WillACosta/wlfkbd/docs/gallery/IMG_1042.JPEG

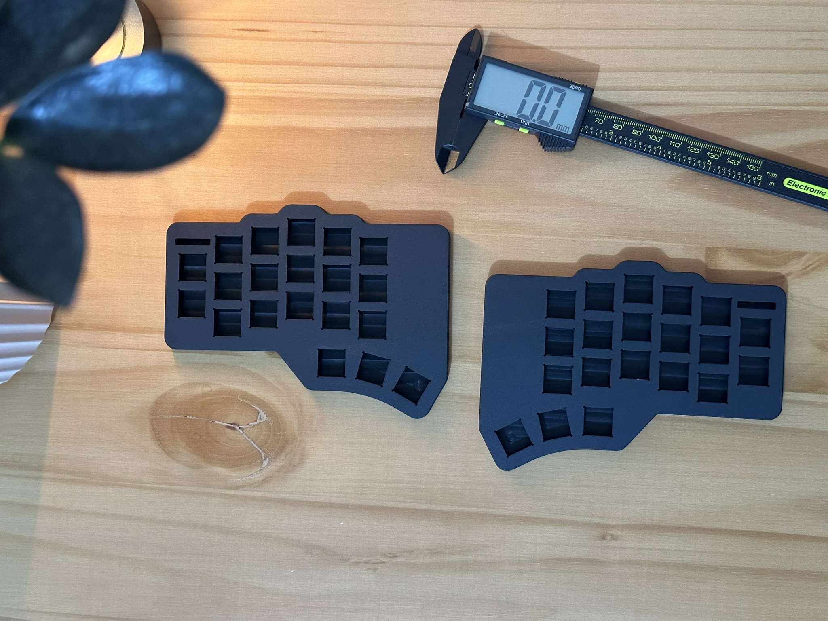
docs/gallery/IMG_1042.JPEG
