WillACosta/wlfkbd/docs/gallery/IMG_1050.JPEG

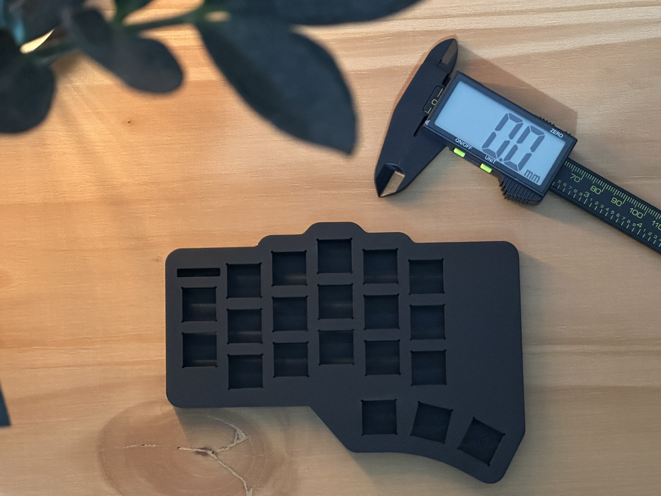
docs/gallery/IMG_1050.JPEG
