WillACosta/wlfkbd/docs/gallery/IMG_1052.JPEG

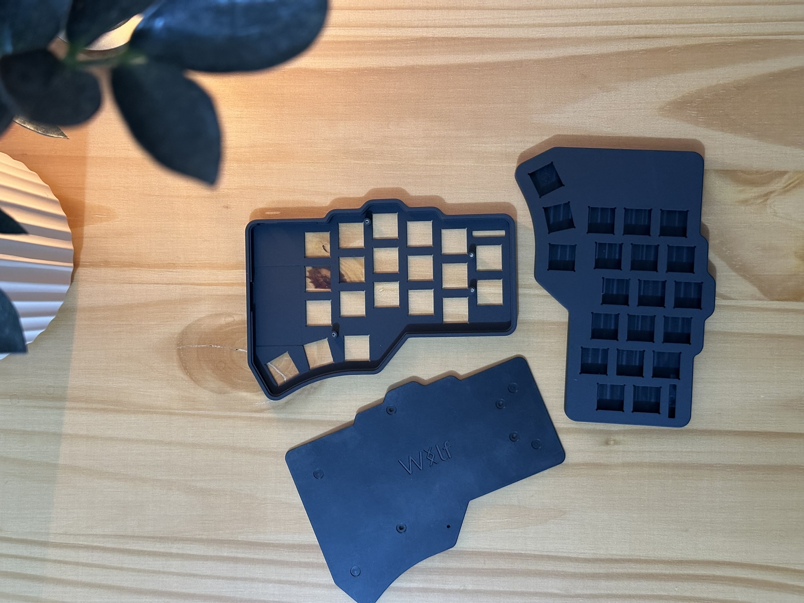
docs/gallery/IMG_1052.JPEG
