WillACosta/wlfkbd/docs/gallery/IMG_1053.JPEG

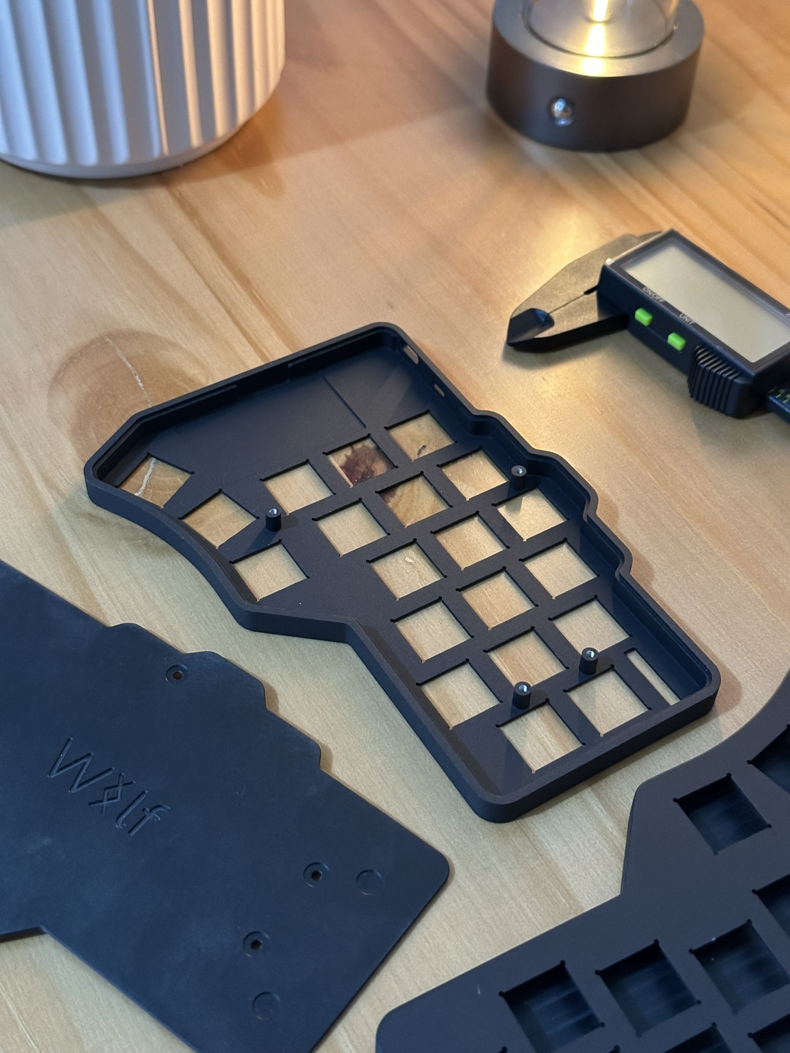
docs/gallery/IMG_1053.JPEG
