WillACosta/wlfkbd/docs/gallery/IMG_1055.JPEG

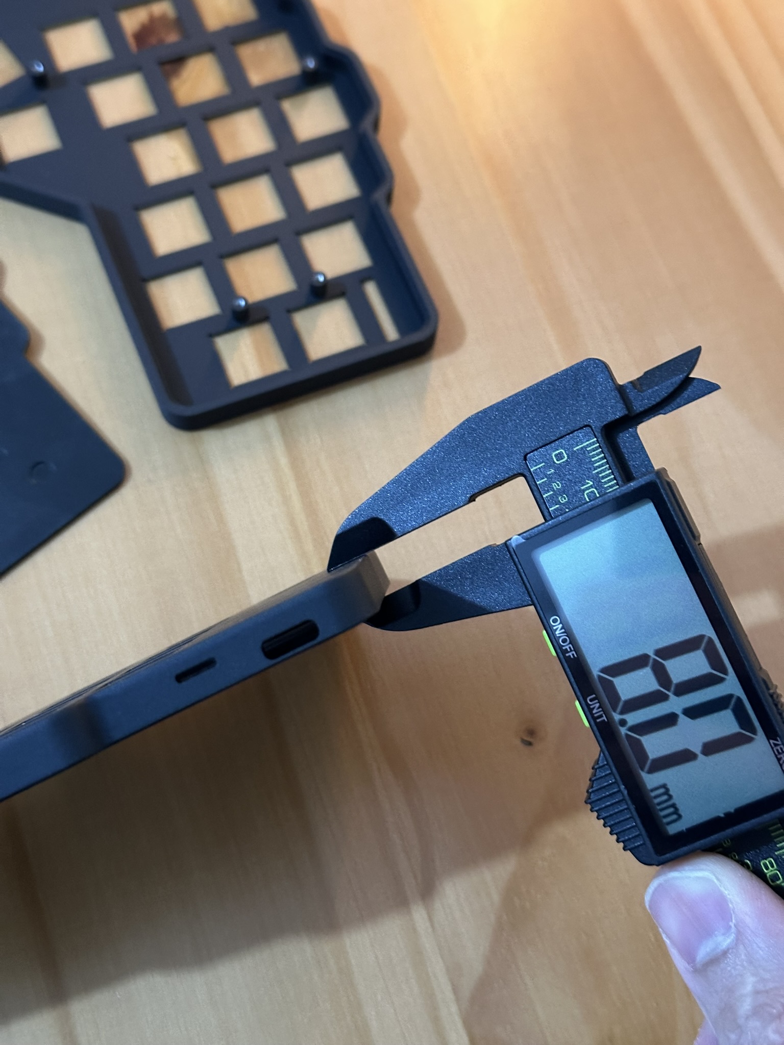
docs/gallery/IMG_1055.JPEG
