WillACosta/wlfkbd/docs/gallery/IMG_1058.JPEG

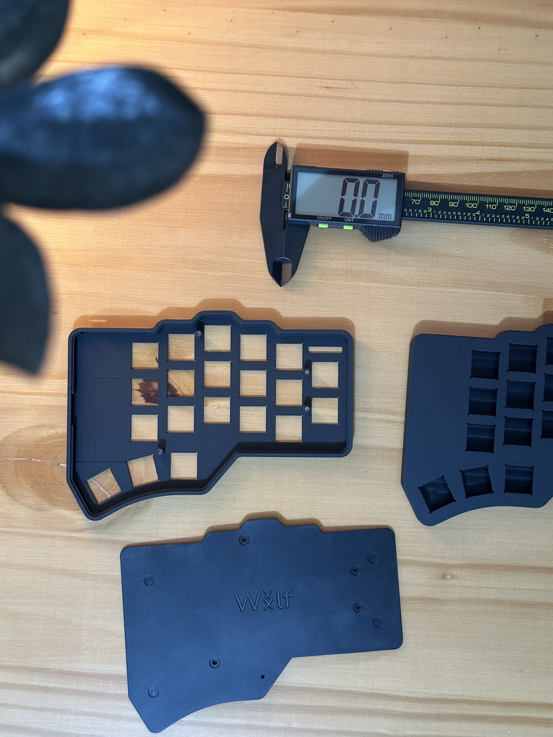
docs/gallery/IMG_1058.JPEG
