WillACosta/wlfkbd/docs/gallery/IMG_1061.JPEG

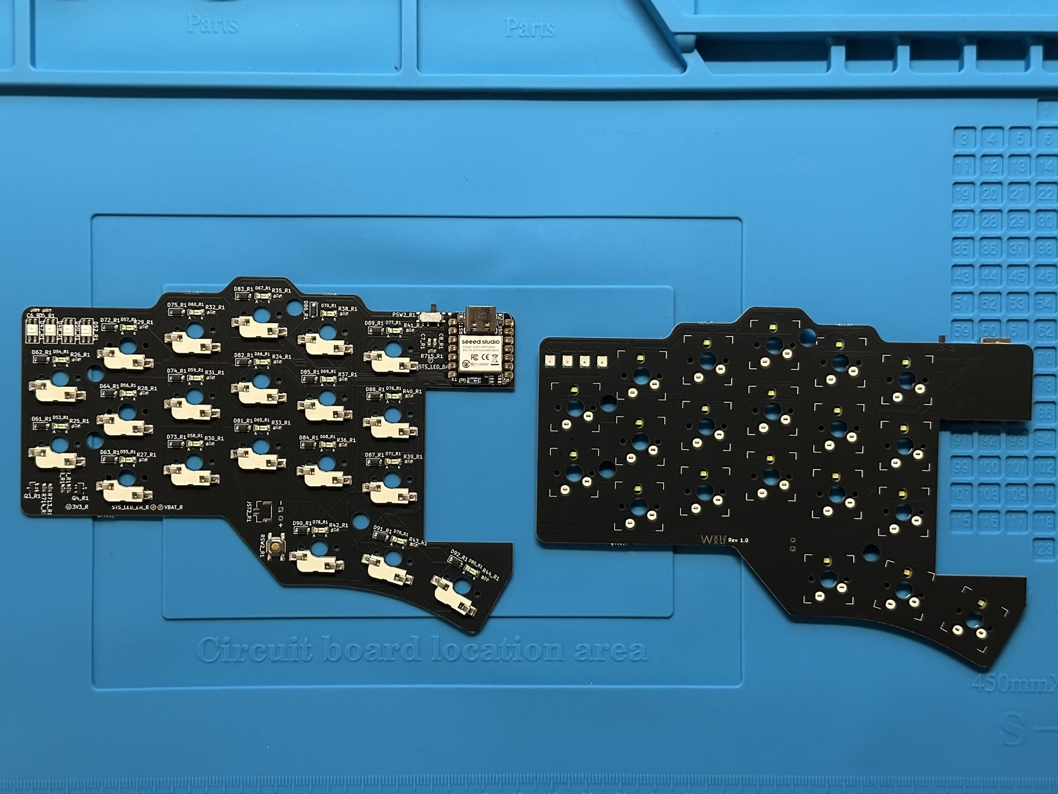
docs/gallery/IMG_1061.JPEG
