WillACosta/wlfkbd/docs/gallery/IMG_1062.JPEG

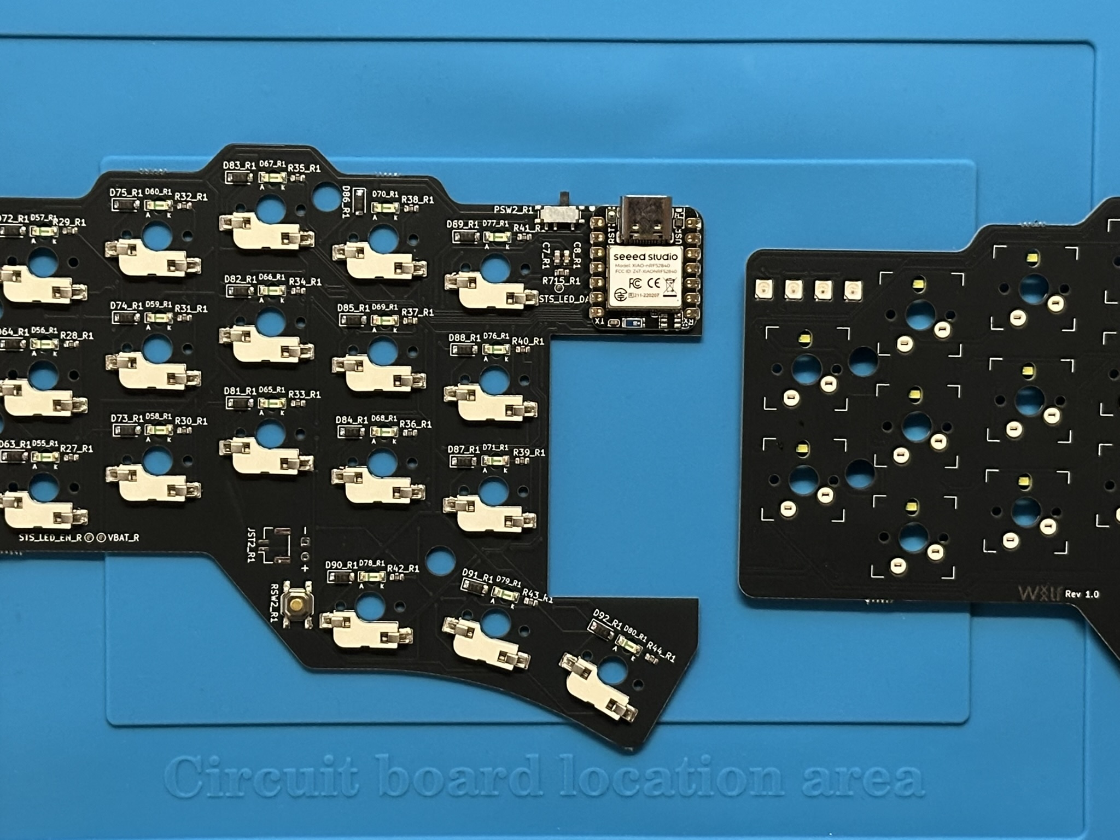
docs/gallery/IMG_1062.JPEG
