WillACosta/wlfkbd/docs/gallery/IMG_1063.JPEG

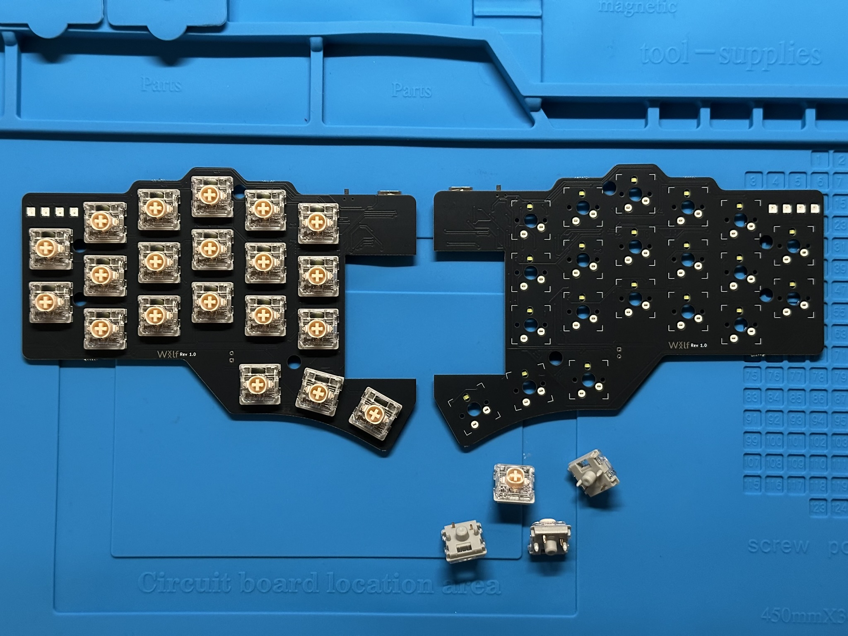
docs/gallery/IMG_1063.JPEG
