WillACosta/wlfkbd/docs/gallery/IMG_1074.JPEG

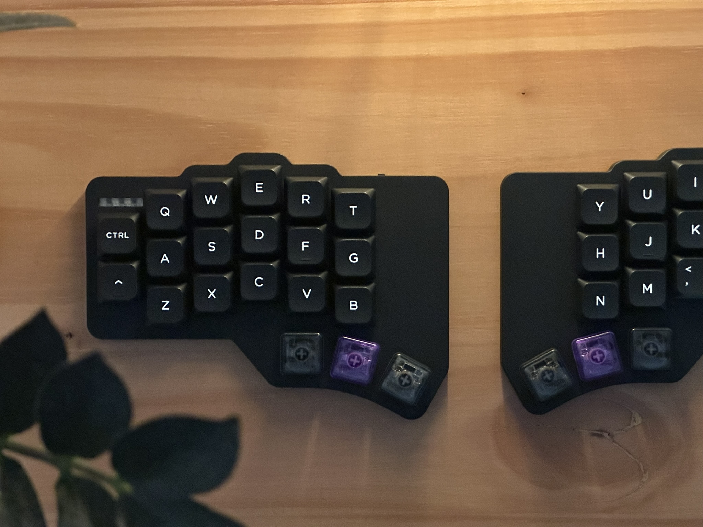
docs/gallery/IMG_1074.JPEG
