WillACosta/wlfkbd/docs/gallery/IMG_1075.JPEG

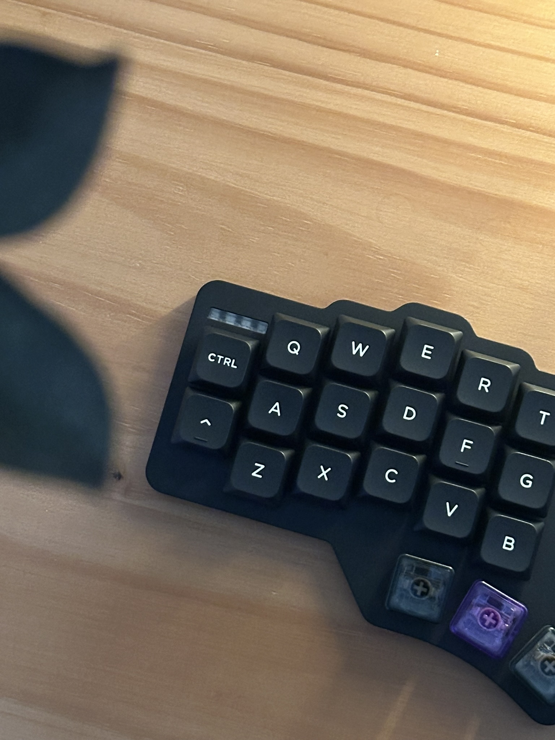
docs/gallery/IMG_1075.JPEG
