WillACosta/wlfkbd/docs/gallery/IMG_1085.JPEG

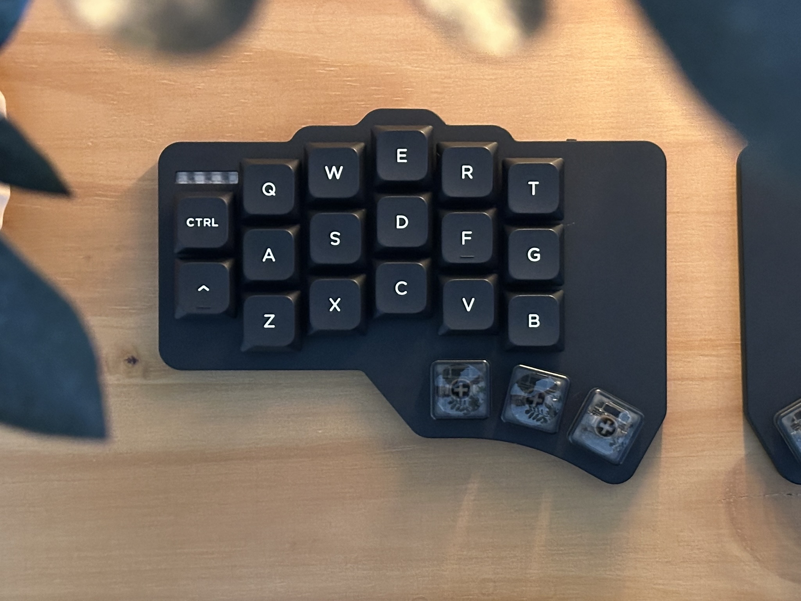
docs/gallery/IMG_1085.JPEG
