WillACosta/wlfkbd/docs/gallery/IMG_1086.JPEG

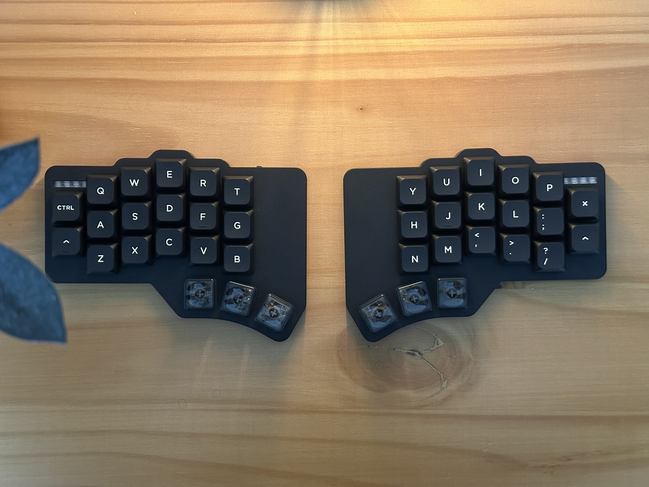
docs/gallery/IMG_1086.JPEG
