WillACosta/wlfkbd/docs/gallery/IMG_1089.JPEG

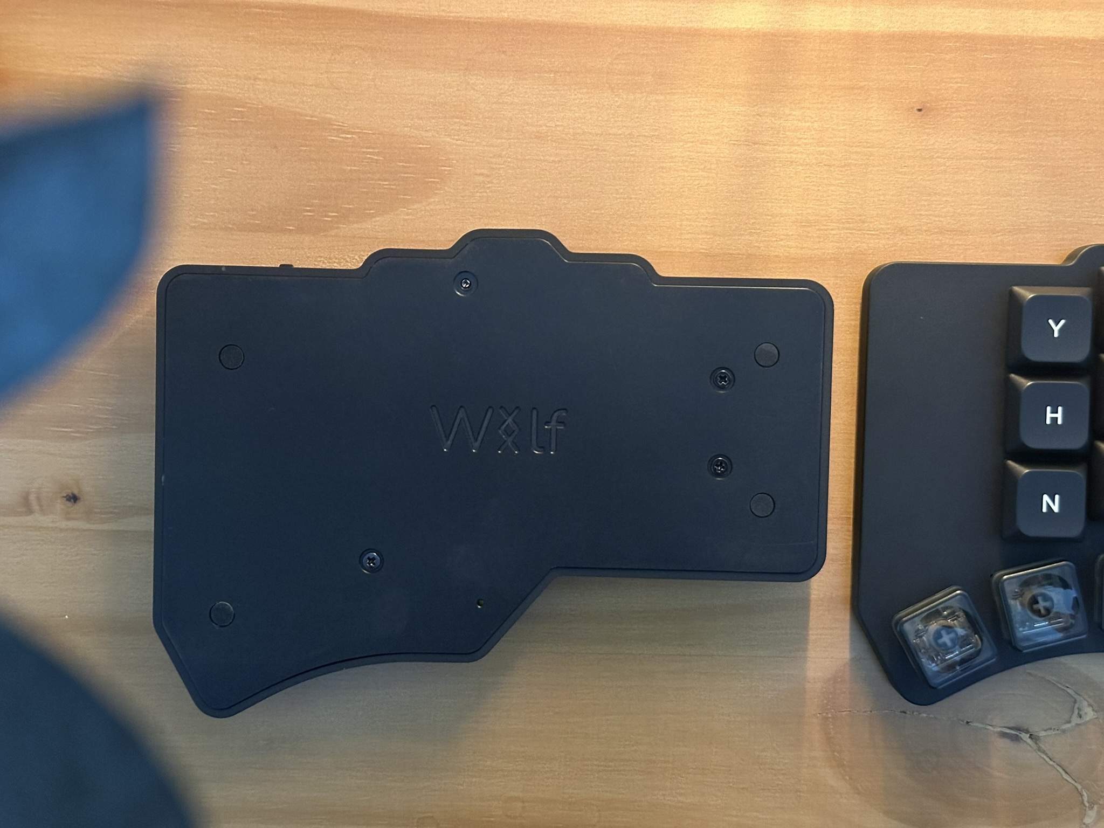
docs/gallery/IMG_1089.JPEG
