WillACosta/wlfkbd/docs/gallery/IMG_1092.JPEG

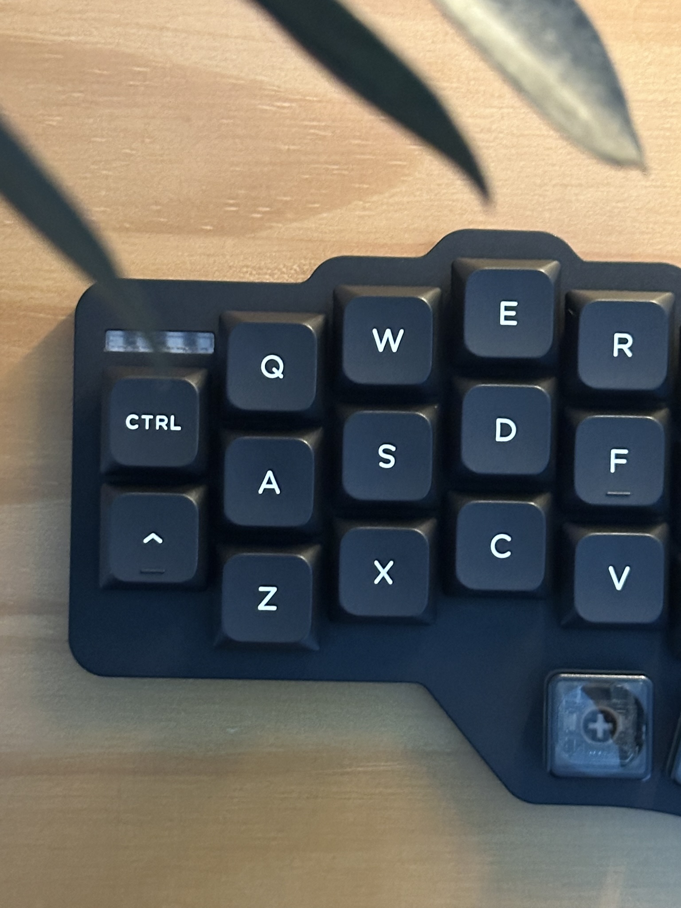
docs/gallery/IMG_1092.JPEG
