WillACosta/wlfkbd/docs/gallery/IMG_1093.JPG

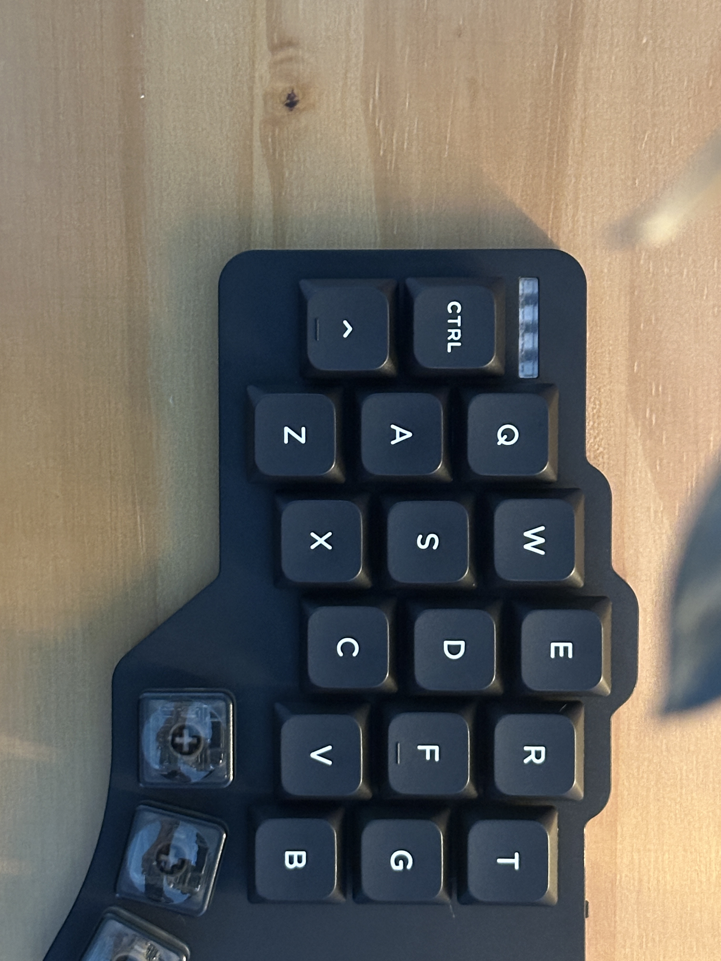
docs/gallery/IMG_1093.JPG
