WillACosta/wlfkbd/docs/gallery/IMG_1097.JPEG

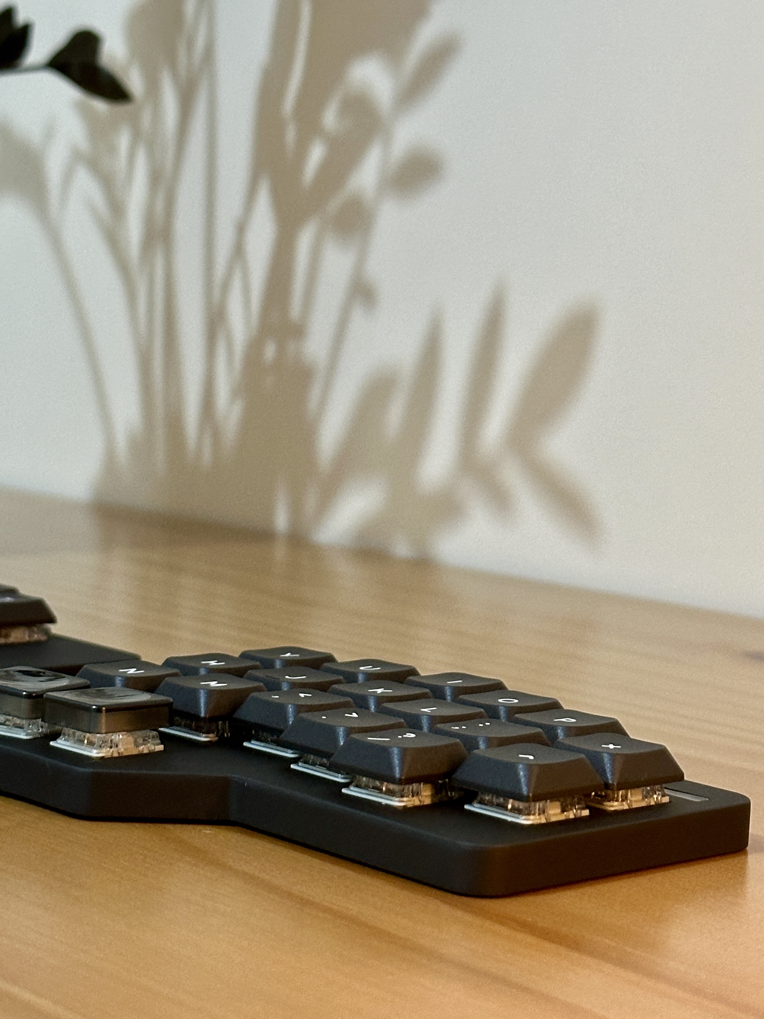
docs/gallery/IMG_1097.JPEG
