WillACosta/wlfkbd/docs/gallery/IMG_1100.JPG

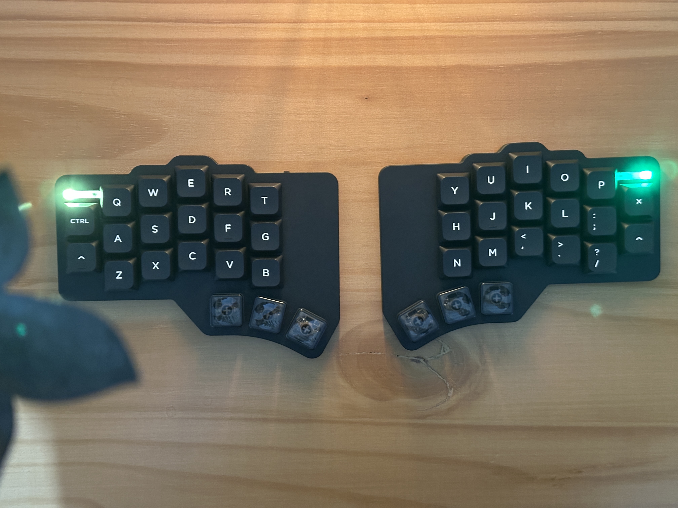
docs/gallery/IMG_1100.JPG
