WillACosta/wlfkbd/docs/gallery/IMG_1102.JPEG

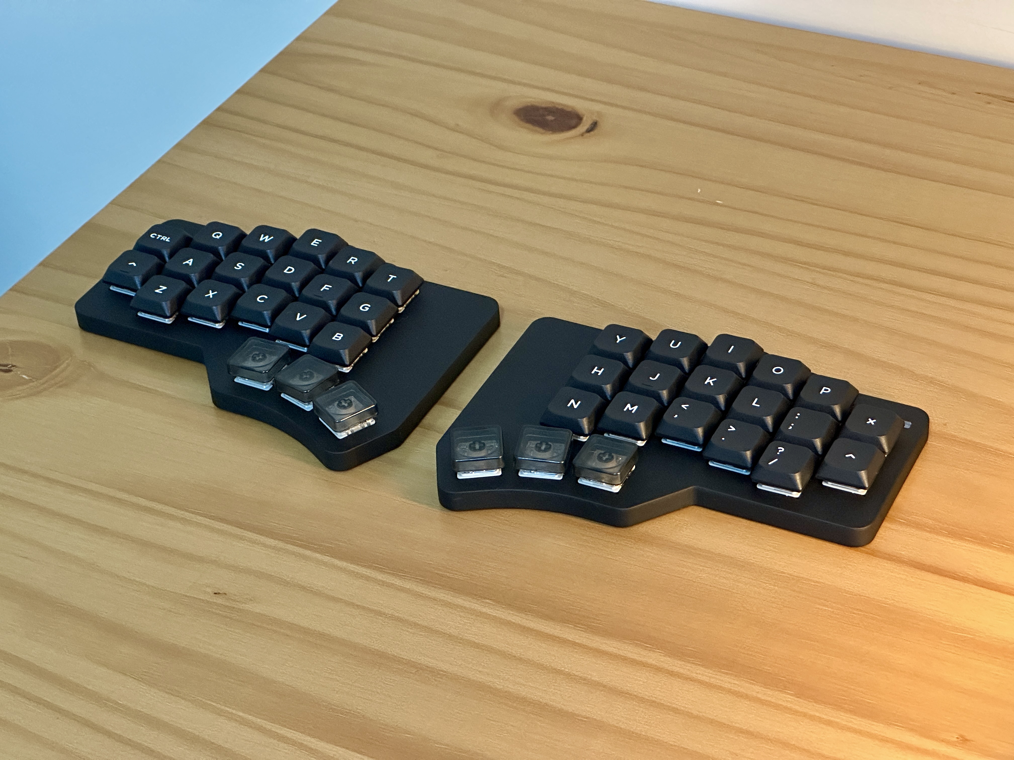
docs/gallery/IMG_1102.JPEG
