WillACosta/wlfkbd/docs/gallery/IMG_1107.JPG

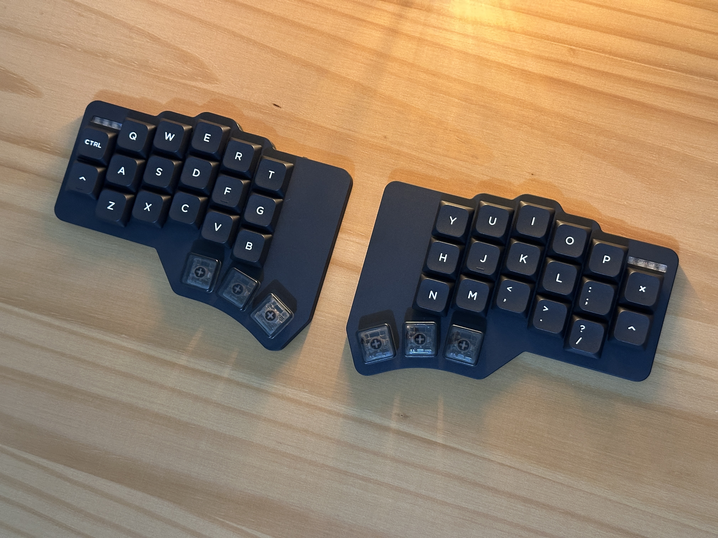
docs/gallery/IMG_1107.JPG
