WillACosta/wlfkbd/docs/gallery/IMG_1114.JPG

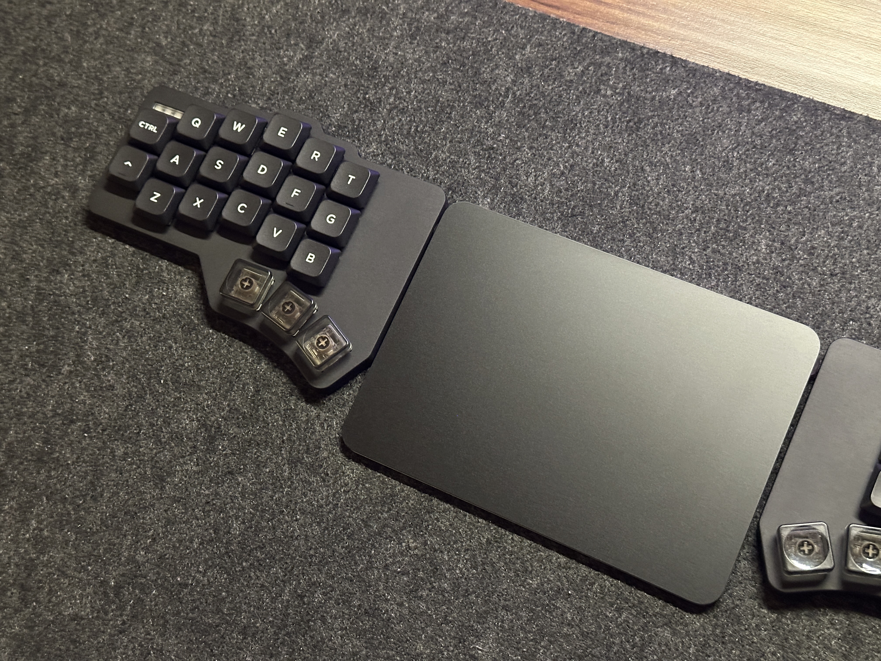
docs/gallery/IMG_1114.JPG
