WillACosta/wlfkbd/docs/gallery/IMG_1119.JPEG

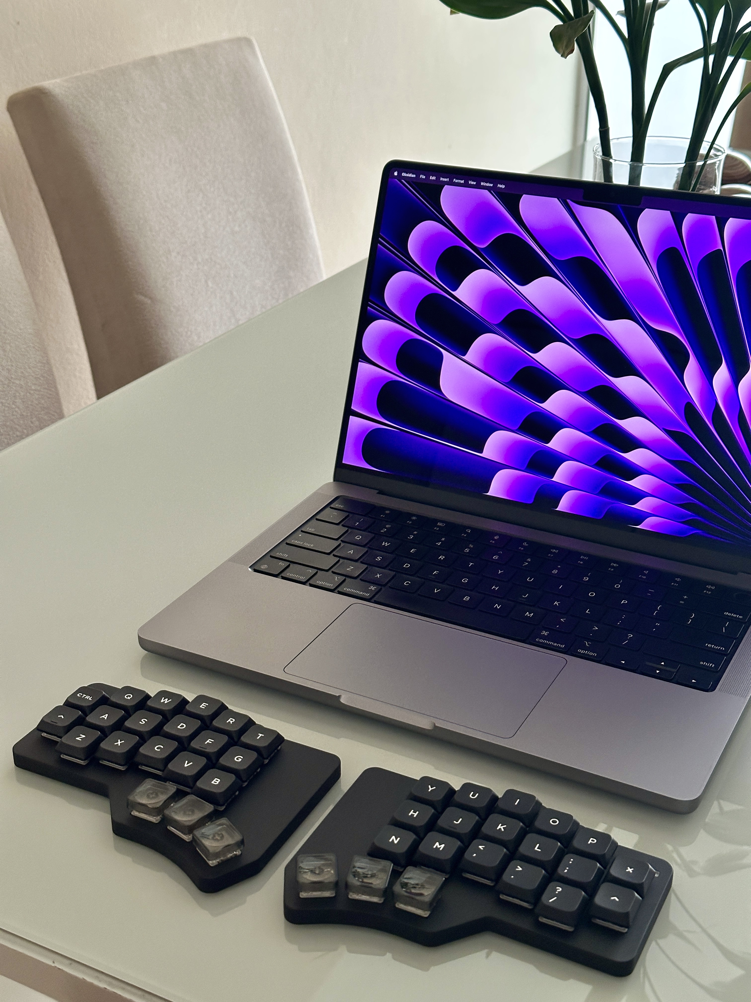
docs/gallery/IMG_1119.JPEG
