WillACosta/wlfkbd/docs/gallery/IMG_1120.JPG

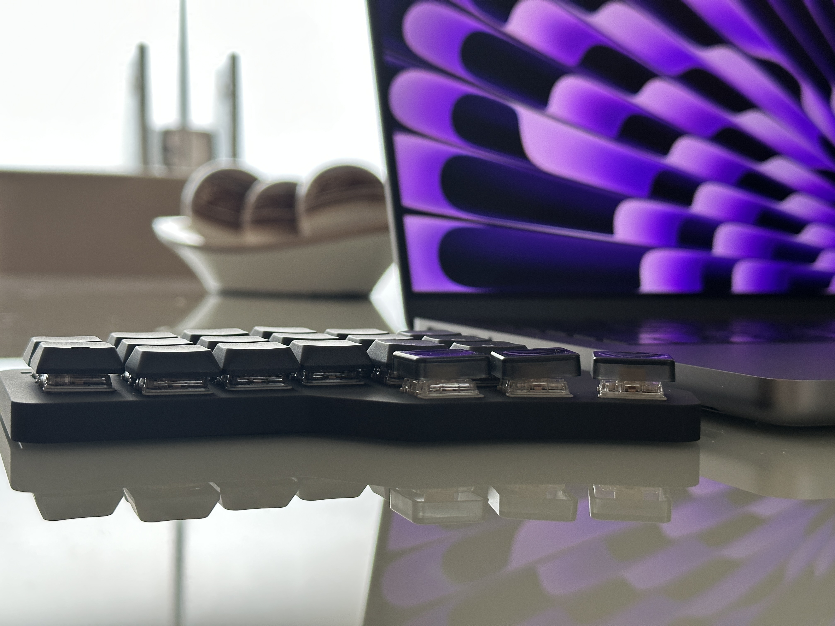
docs/gallery/IMG_1120.JPG
