WillACosta/wlfkbd/docs/gallery/IMG_1122.JPG

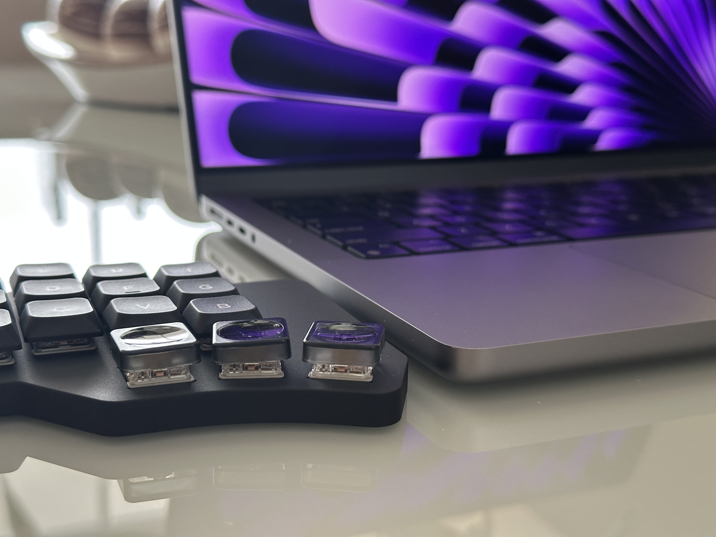
docs/gallery/IMG_1122.JPG
