WillACosta/wlfkbd/docs/gallery/IMG_1124.JPG

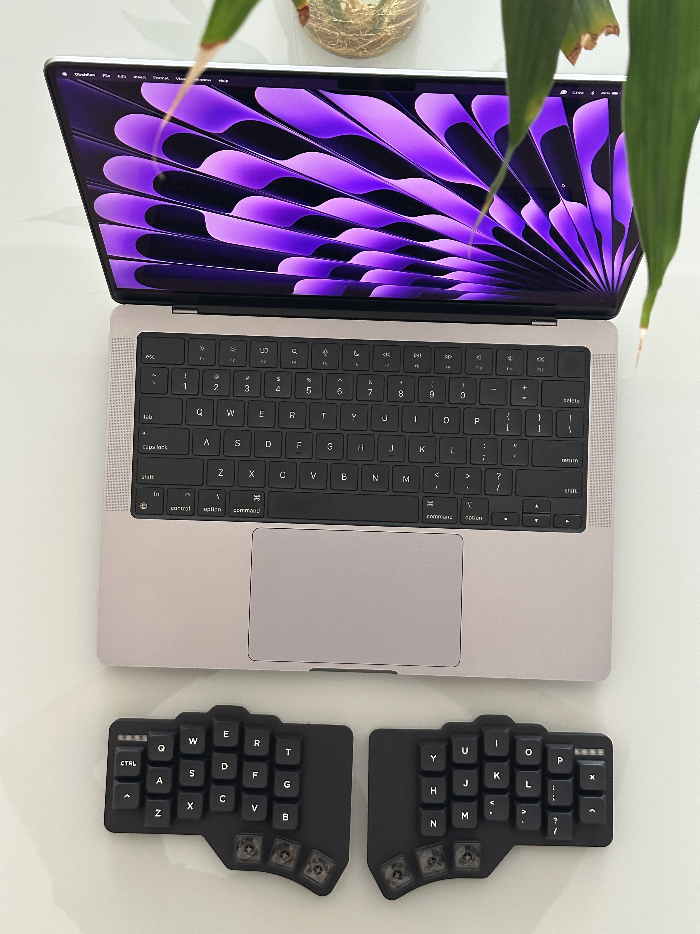
docs/gallery/IMG_1124.JPG
