WillACosta/wlfkbd/docs/gallery/IMG_1191.JPG

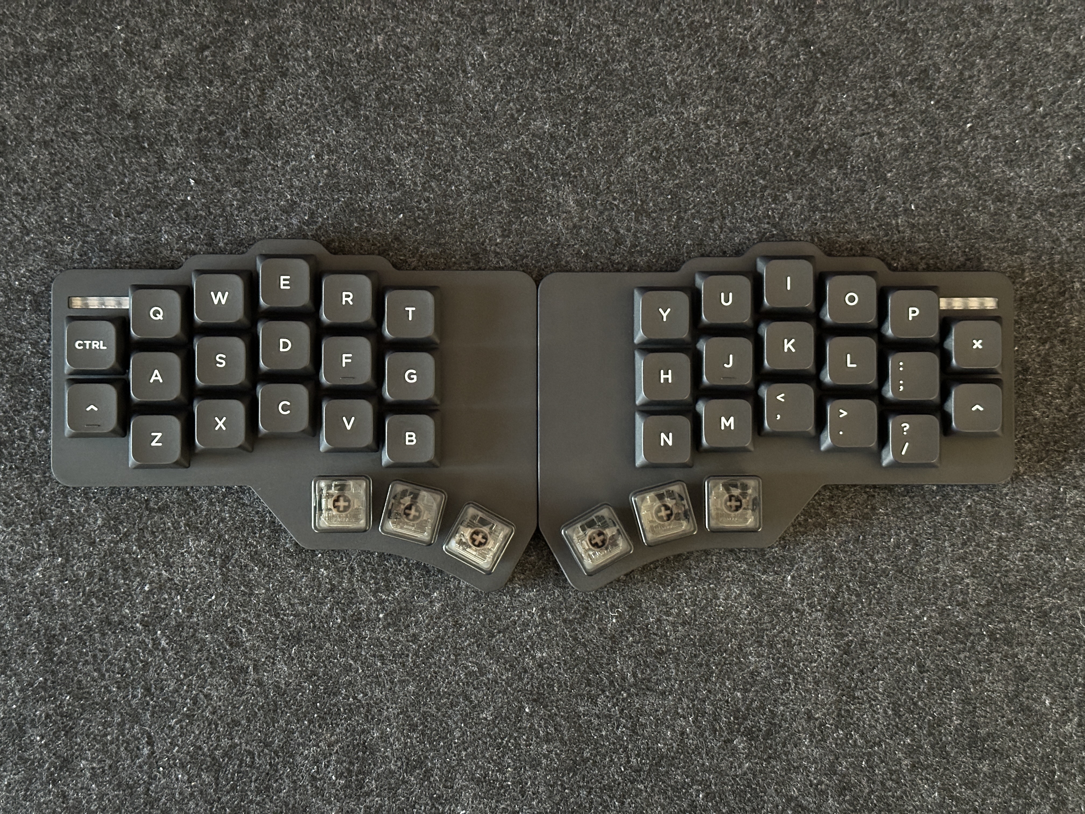
docs/gallery/IMG_1191.JPG
