WillACosta/wlfkbd/docs/gallery/IMG_1196.JPG

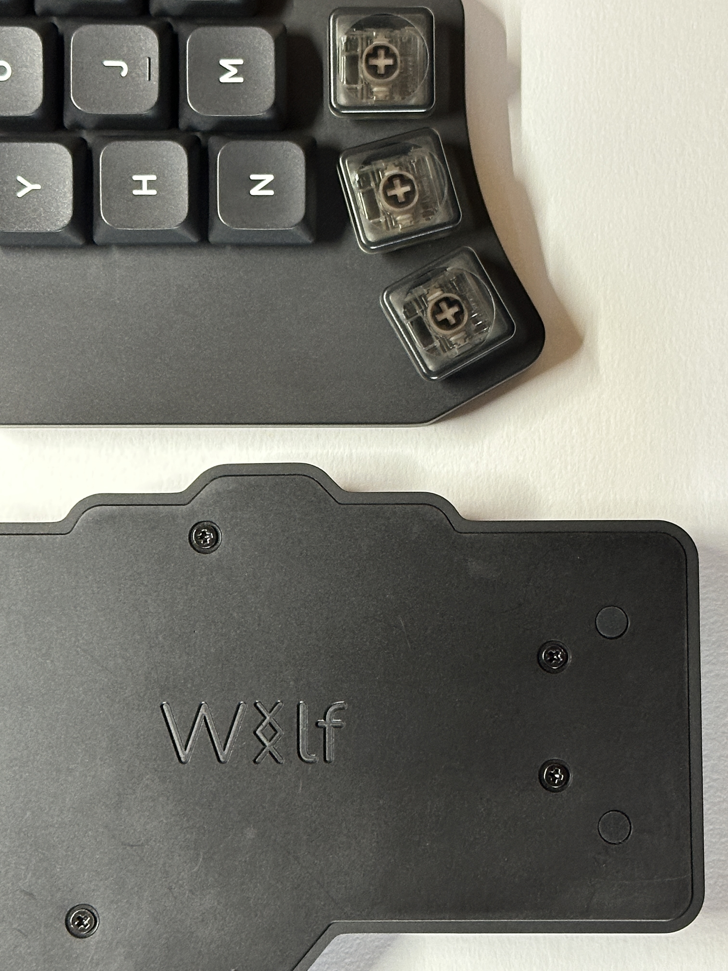
docs/gallery/IMG_1196.JPG
