WillACosta/wlfkbd/docs/gallery/IMG_1203.JPG

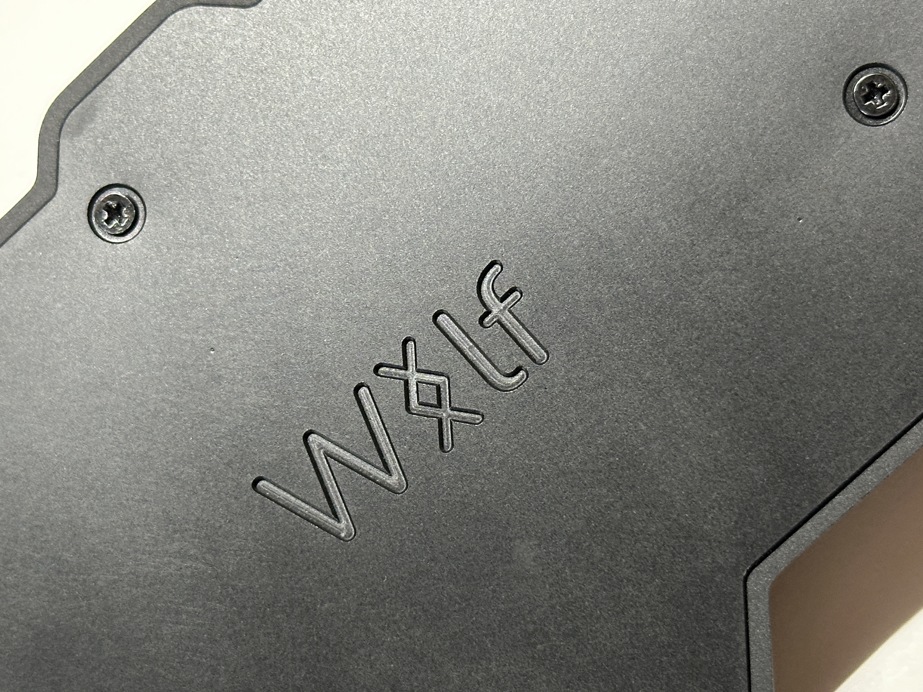
docs/gallery/IMG_1203.JPG
