WillACosta/wlfkbd/docs/gallery/IMG_1206.JPG

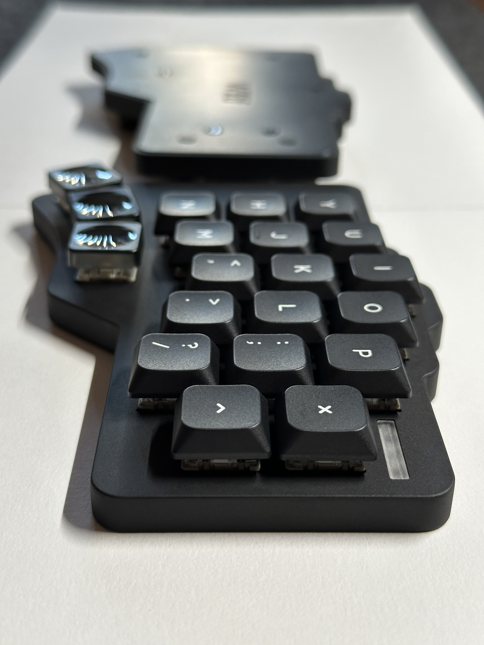
docs/gallery/IMG_1206.JPG
