WillACosta/wlfkbd/docs/gallery/IMG_1207.JPG

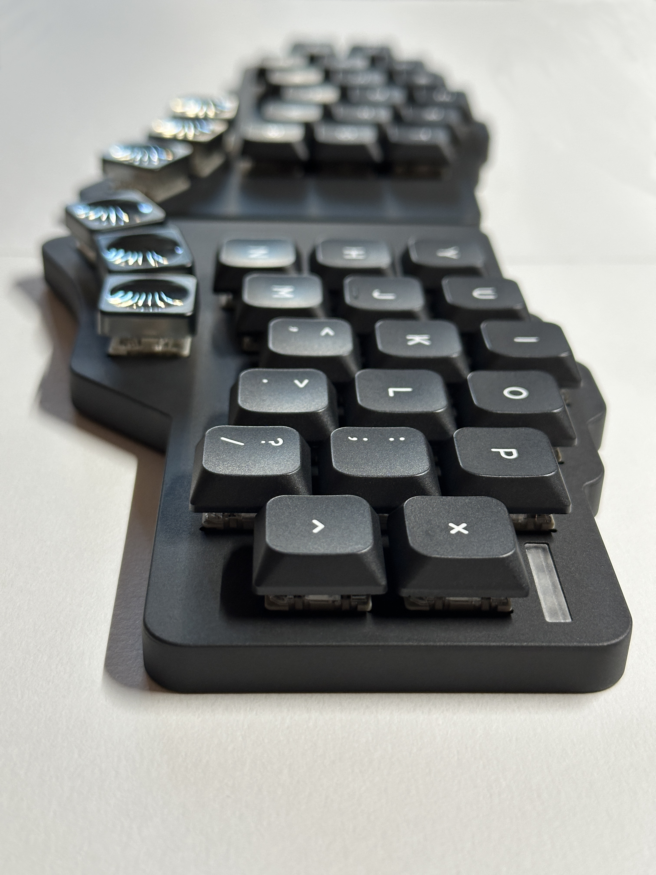
docs/gallery/IMG_1207.JPG
