WillACosta/wlfkbd/docs/gallery/IMG_1210.JPG

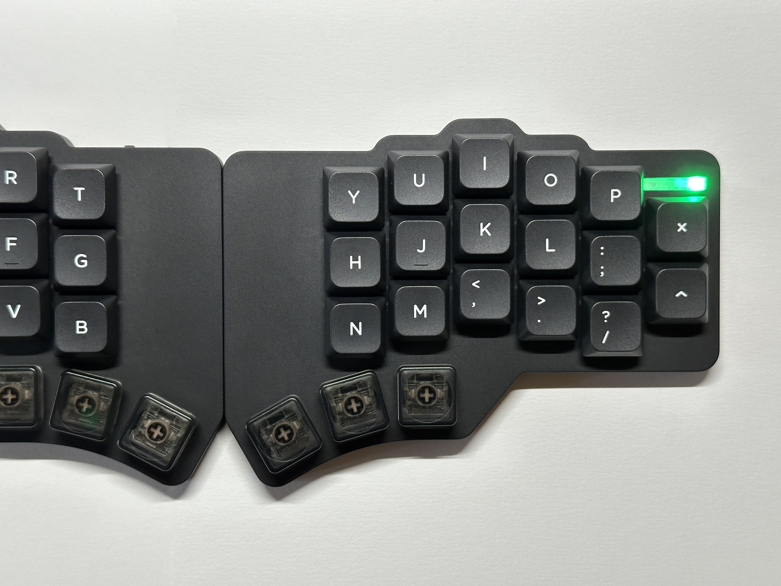
docs/gallery/IMG_1210.JPG
