WillACosta/wlfkbd/docs/gallery/IMG_1212.JPG

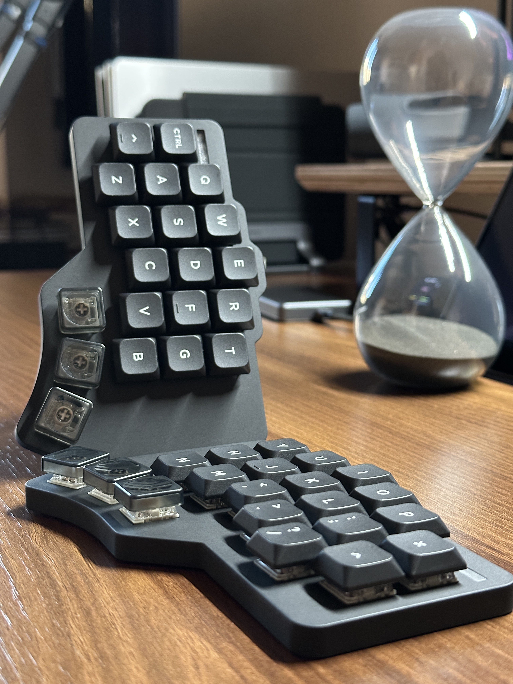
docs/gallery/IMG_1212.JPG
