WillACosta/wlfkbd/docs/gallery/IMG_1224.JPG

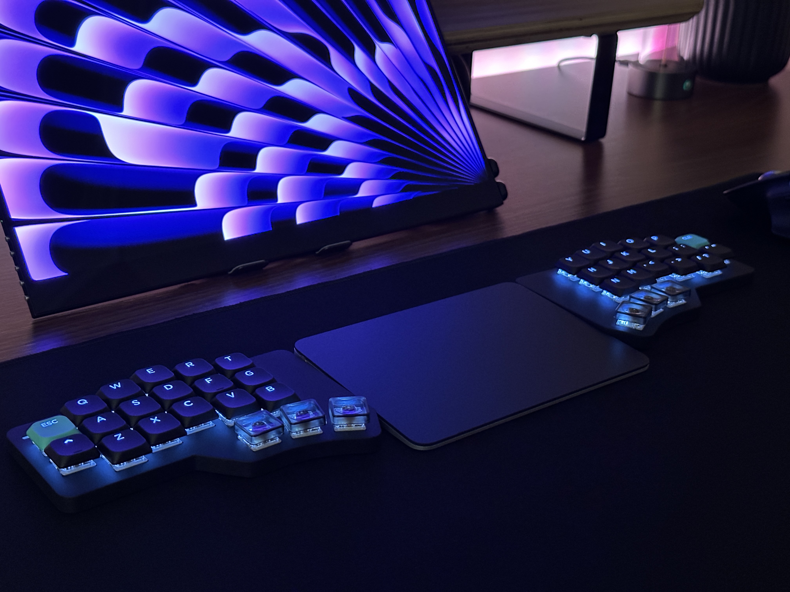
docs/gallery/IMG_1224.JPG
