WillACosta/wlfkbd/docs/gallery/IMG_1226.JPG

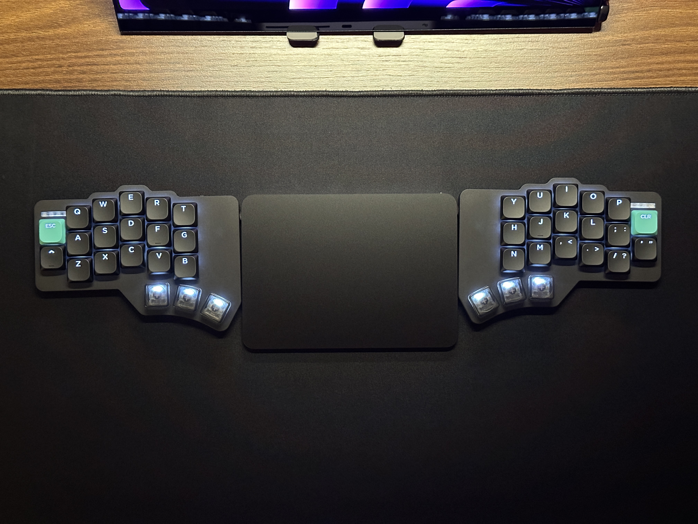
docs/gallery/IMG_1226.JPG
