WillACosta/wlfkbd/docs/gallery/IMG_1228.JPG

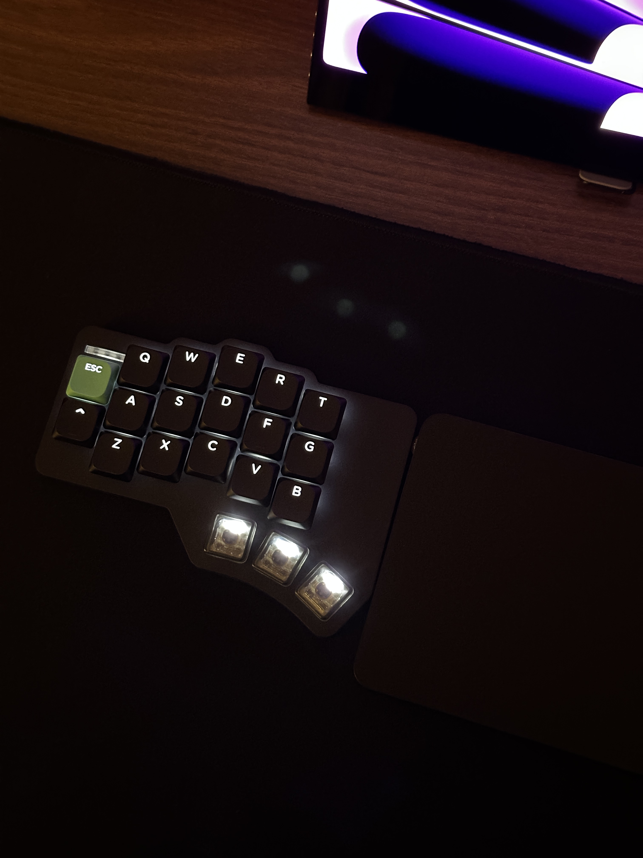
docs/gallery/IMG_1228.JPG
