WillACosta/wlfkbd/docs/renders/keycaps/back.png

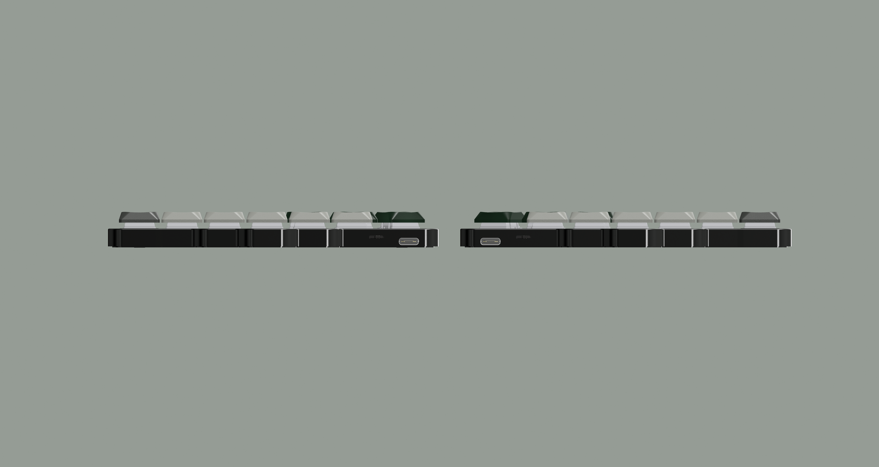
docs/renders/keycaps/back.png
