WillACosta/wlfkbd/docs/renders/keycaps/back_angled.png

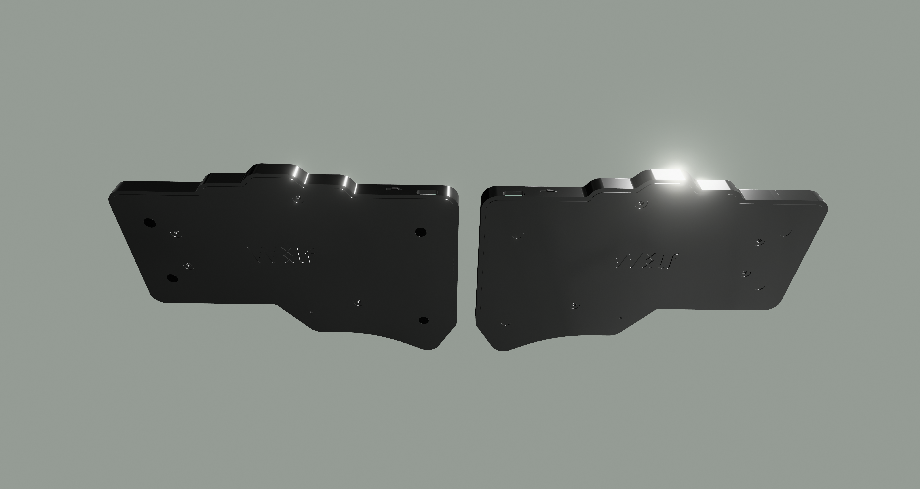
docs/renders/keycaps/back_angled.png
