WillACosta/wlfkbd/docs/renders/keycaps/left_corner.png

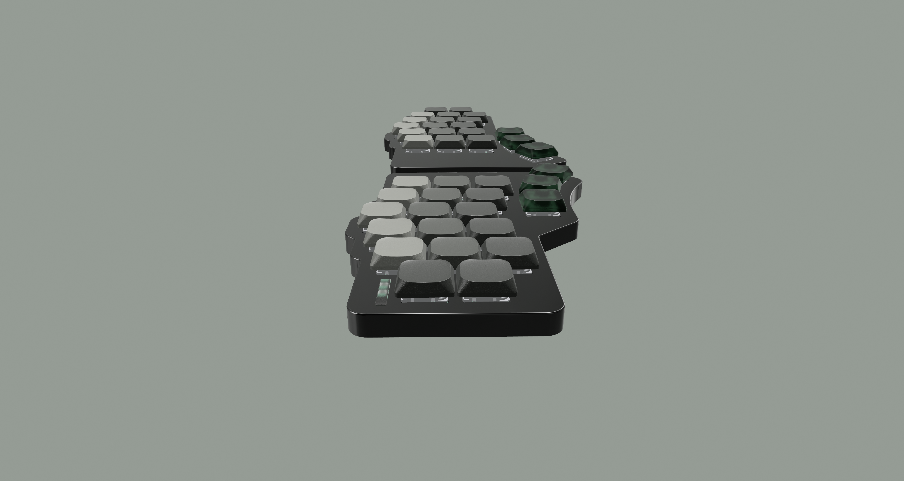
docs/renders/keycaps/left_corner.png
