WillACosta/wlfkbd/docs/renders/media/wlfkbd_left_angled.png

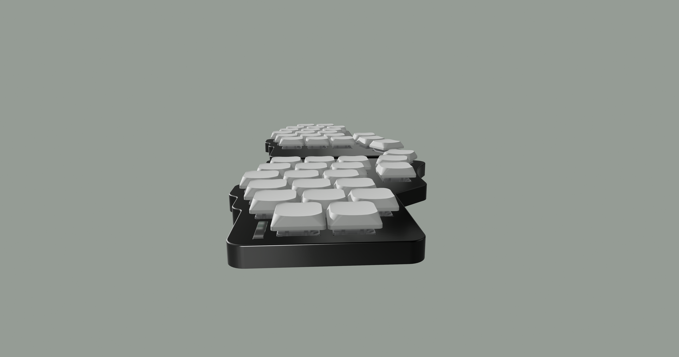
docs/renders/media/wlfkbd_left_angled.png
