WillACosta/wlfkbd/docs/renders/media/wlfkbd_wireframe.png

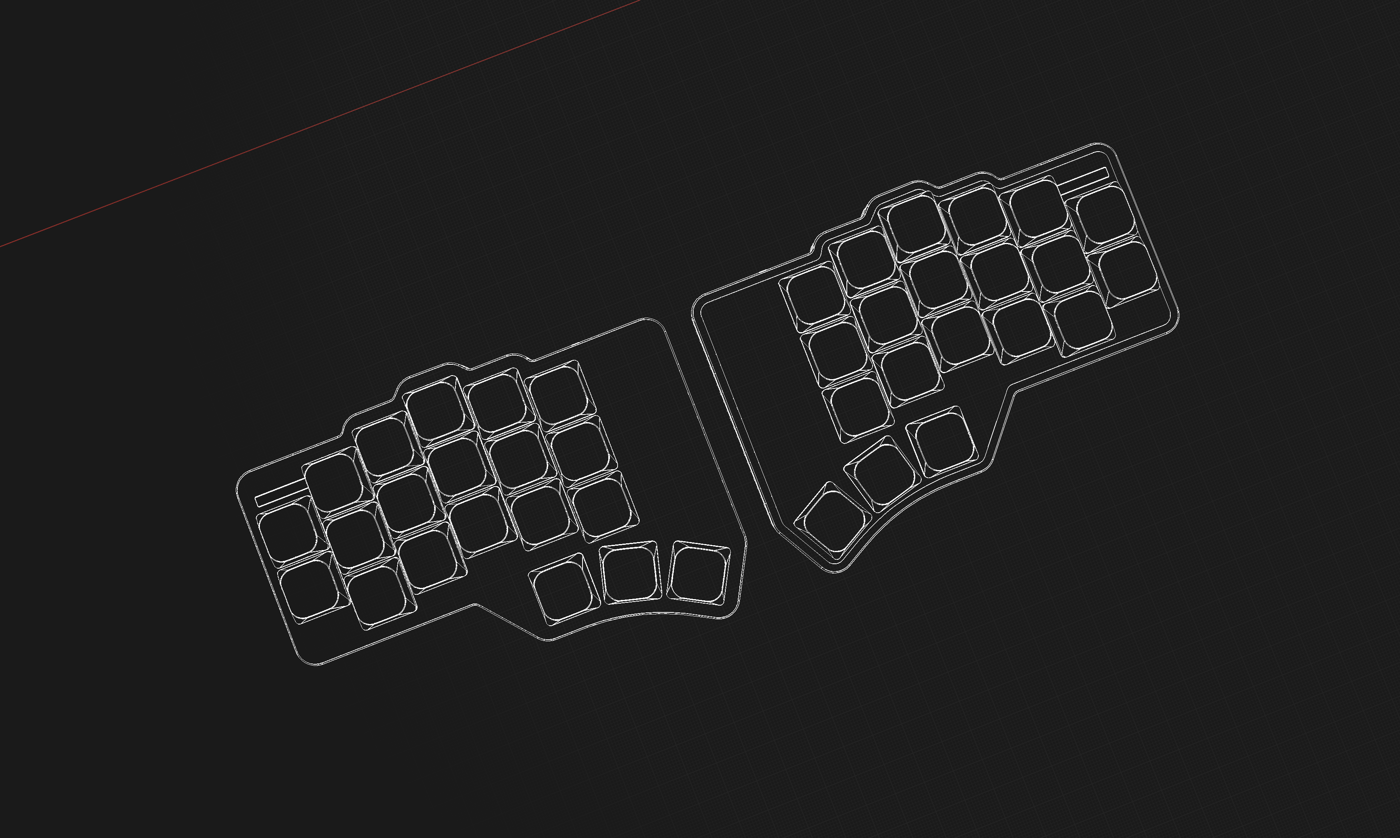
docs/renders/media/wlfkbd_wireframe.png
