WillACosta/wlfkbd/docs/renders/media/wlfkbd_wireframe_3d.png

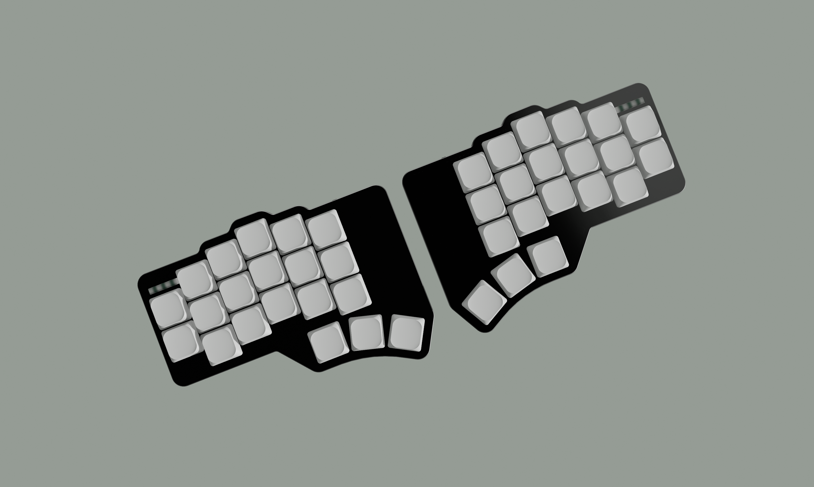
docs/renders/media/wlfkbd_wireframe_3d.png
