WillACosta/wlfkbd/docs/gallery/IMG_1213.JPG

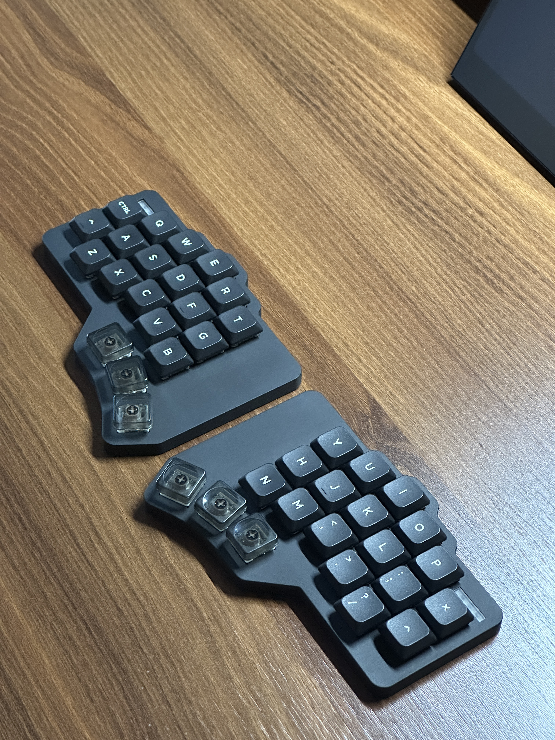
docs/gallery/IMG_1213.JPG
