WillACosta/wlfkbd/docs/gallery/IMG_1219.JPG

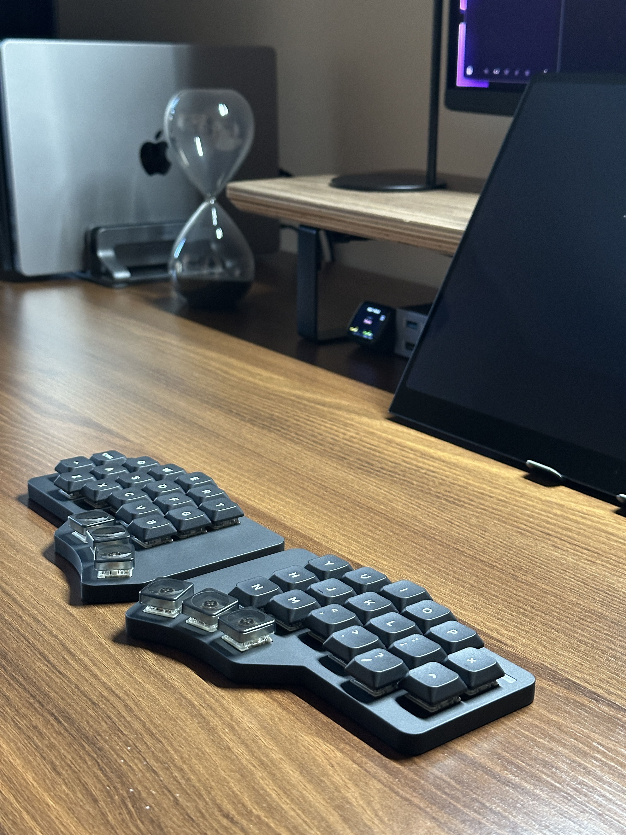
docs/gallery/IMG_1219.JPG
