WillACosta/wlfkbd/docs/gallery/IMG_1223.JPG

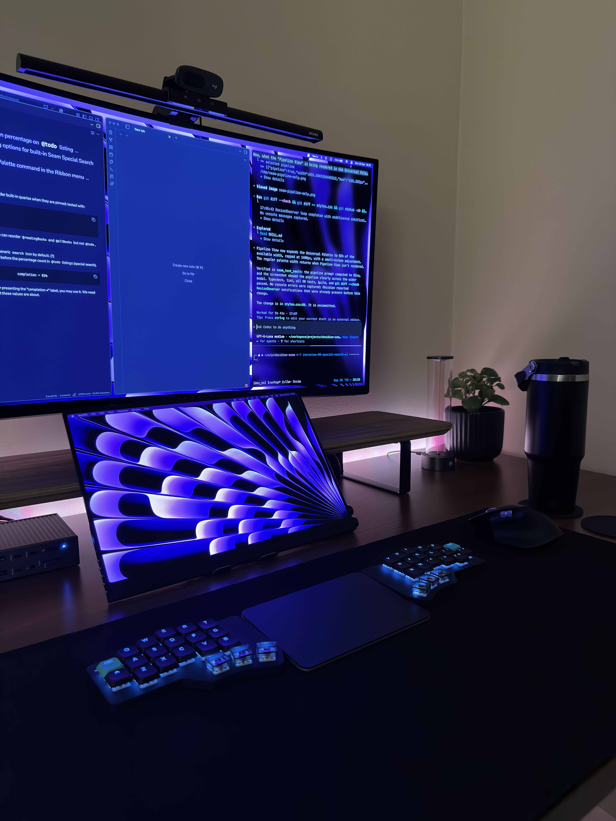
docs/gallery/IMG_1223.JPG
