WillACosta/wlfkbd/docs/renders/keycaps/top_close.png

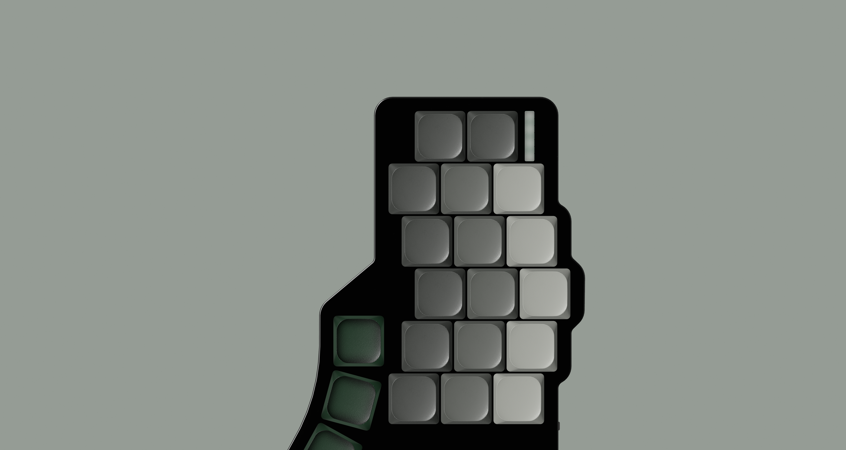
docs/renders/keycaps/top_close.png
