WillACosta/wlfkbd/docs/renders/keycaps/top_corner.png

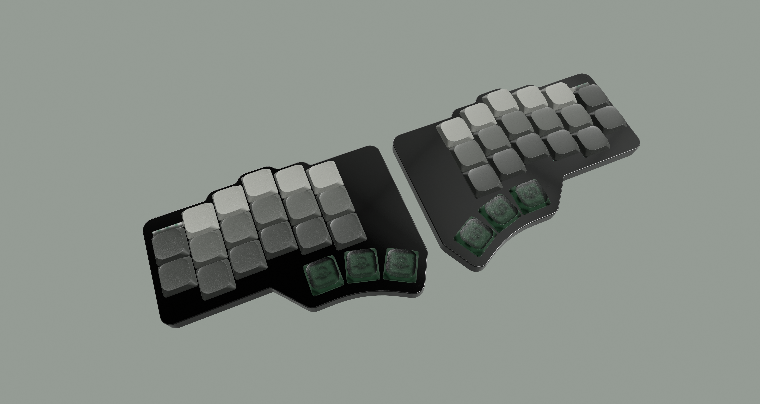
docs/renders/keycaps/top_corner.png
